Ru0110/EE344/Test/WaveformData.csv

_id | Time | Waveform Buffer
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
