Ru0110/EE344/Test/sample_sensor.csv

Time (ms) | RMS Voltage (V) | VBrms | RMS Current (A) | IBrms | Power (W) | PowerB | Power factor | PfB | Frequency (Hz) | FrequencyB | Temperature (C) | Pressure (Pa) | Humidity (%) | Emergency Status
50477 | 0.027175210416316986 | 1.969692349433899 | 0.0 | 0.0 | 0.0 | 0.0 | 1.0 | 1.0 | 49.999996185302734 | 49.94847869873047 | 31.236751556396484 | 100103.125 | 36.60318374633789 | 0
50944 | 0.027228936553001404 | 1.9664041996002197 | 0.0 | 0.0 | 0.0 | 0.0 | 1.0 | 1.0 | 49.999996185302734 | 50.049076080322266 | 31.231670379638672 | 100099.546875 | 36.597412109375 | 0
51411 | 0.02669166587293148 | 1.9588608741760254 | 0.0 | 0.0 | 0.0 | 0.0 | 1.0 | 1.0 | 49.999996185302734 | 50.160545349121094 | 31.241836547851562 | 100106.6875 | 36.63225173950195 | 0
51878 | 0.026551974937319756 | 1.9410665035247803 | 0.0 | 0.0 | 0.0 | 0.0 | 1.0 | 1.0 | 49.999996185302734 | 50.00682830810547 | 31.231670379638672 | 100099.546875 | 36.67314147949219 | 0
52345 | 0.027228936553001404 | 1.949920654296875 | 0.0 | 0.0 | 0.0 | 0.0 | 1.0 | 1.0 | 49.999996185302734 | 50.11634826660156 | 31.226587295532227 | 100098.71875 | 36.70813751220703 | 0
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
