Ru0110/EE344/Software/RP2040_code/tcp_server.h

#include <string.h>
#include <stdlib.h>

#include "pico/stdlib.h"
#include "pico/cyw43_arch.h"

#include "lwip/pbuf.h"
#include "lwip/tcp.h"

#define TCP_PORT 4242
#define DEBUG_printf printf
#define BUF_SIZE 512
#define TEST_ITERATIONS 10
#define POLL_TIME_S 3

typedef struct TCP_SERVER_T_ {
    struct tcp_pcb *server_pcb;
    struct tcp_pcb *client_pcb;
    bool complete;
    uint8_t buffer_sent[BUF_SIZE];
    uint8_t buffer_recv[BUF_SIZE];
    int sent_len;
    int recv_len;
    int run_count;
} TCP_SERVER_T;

TCP_SERVER_T* tcp_server_init(void);
err_t tcp_server_close(TCP_SERVER_T *state);
err_t tcp_server_result(void *arg, int status);
err_t tcp_server_sent(void *arg, struct tcp_pcb *tpcb, u16_t len);
err_t tcp_server_send_data(TCP_SERVER_T *state, struct tcp_pcb *tpcb, uint buffer_size);
err_t tcp_server_recv(void *arg, struct tcp_pcb *tpcb, struct pbuf *p, err_t err);
err_t tcp_server_poll(void *arg, struct tcp_pcb *tpcb);
void tcp_server_err(void *arg, err_t err);
err_t tcp_server_accept(void *arg, struct tcp_pcb *client_pcb, err_t err);
bool tcp_server_open(TCP_SERVER_T *state, uint port);
err_t tcp_restart(TCP_SERVER_T *state);
//void run_tcp_server_test(void);
