Ru0110/EE344/Software/RP2040_code/blocking.h

#ifndef _PICO_SDK_CALLBACKS_H_
#define _PICO_SDK_CALLBACKS_H_

#include "callbacks.h"

#ifdef __cplusplus
extern "C" {
#endif

extern const system_callbacks_t pico_callbacks_blocking;

#ifdef __cplusplus
}
#endif

#endif // _PICO_SDK_CALLBACKS_H_
