Ru0110/EE344/Software/RP2040_code/lwipopts.h

#ifndef _LWIPOPTS_H
#define _LWIPOPTS_H

// Generally you would define your own explicit list of lwIP options
// (see https://www.nongnu.org/lwip/2_1_x/group__lwip__opts.html)
//
// This example uses a common include to avoid repetition
#include "lwipopts_common.h"

#endif
